liveboxandy/ZX-Spider-48K-LBA/STP/SM230332-2.stp

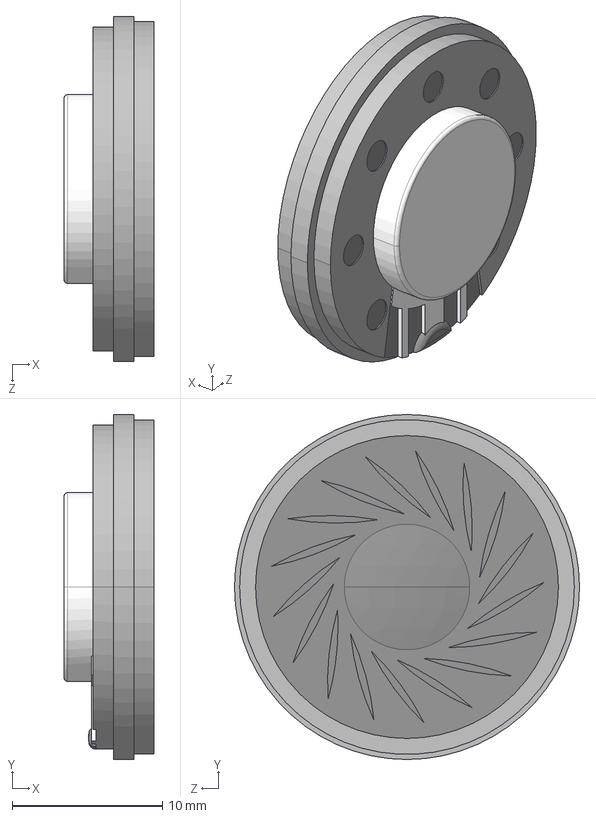
[picture p17: CAD file, 2026-09-20]
STP/SM230332-2.stp
6.00 x 23.0 x 23.0 mm
