liveboxandy/ZX-Spider-48K-LBA/STP/1658998-1.stp

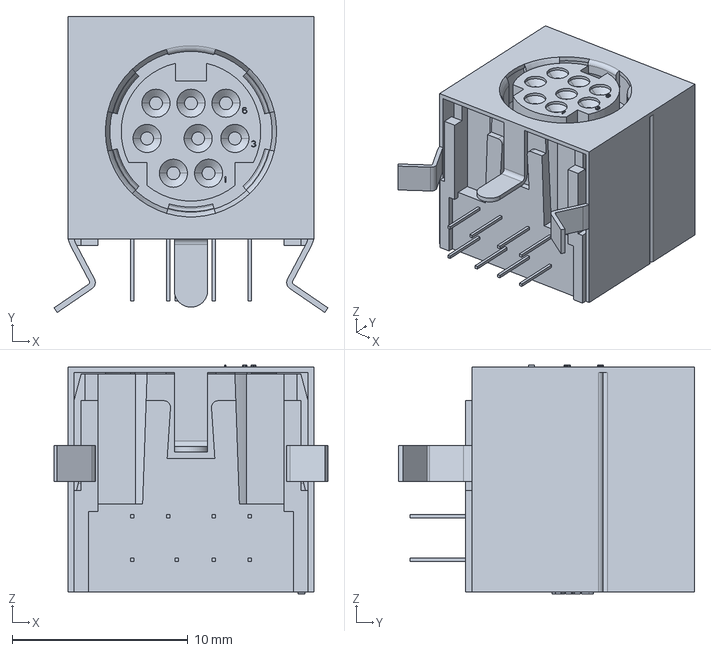
[picture p18: CAD file, 2026-06-21]
STP/1658998-1.stp
15.6 x 16.9 x 13.0 mm
